bcancinov/4-channel-adc-module/step/EEHZA1E680XP.stp

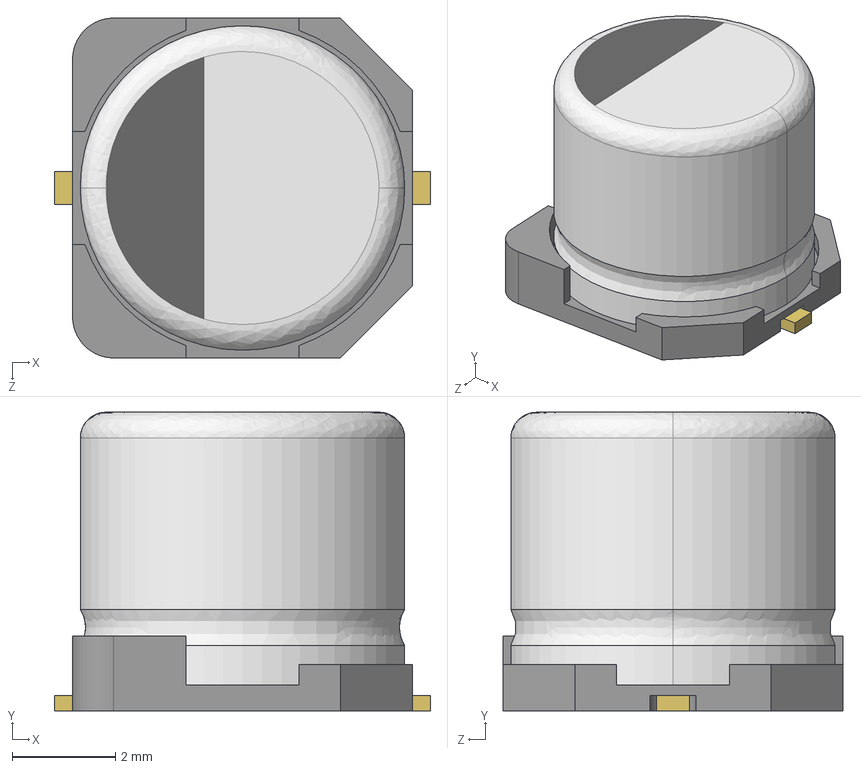
[picture p18: CAD file, 2025-04-16]
step/EEHZA1E680XP.stp
7.30 x 5.80 x 6.60 mm
•W€SIZE CODE D-001_1
•W€SIZE CODE D-002_1
•W€SIZE CODE D-003_1 x 2
