bcancinov/4-channel-adc-module/step/LFCSP16_ADA4945-1ACPZ-R2_ADI.step

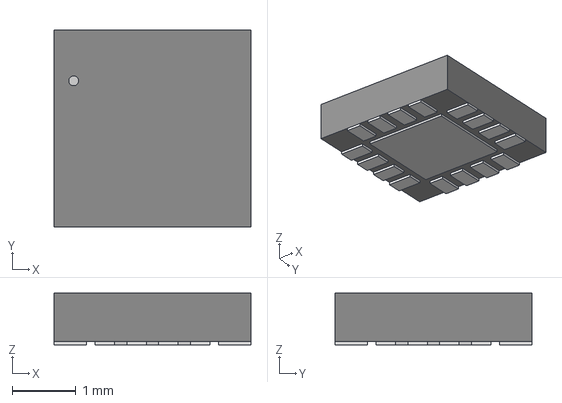
[picture p19: CAD file, 2025-04-16]
step/LFCSP16_ADA4945-1ACPZ-R2_ADI.step
3.10 x 3.10 x 0.815 mm
