bcancinov/4-channel-adc-module/step/24LC16BT-I_OT.stp

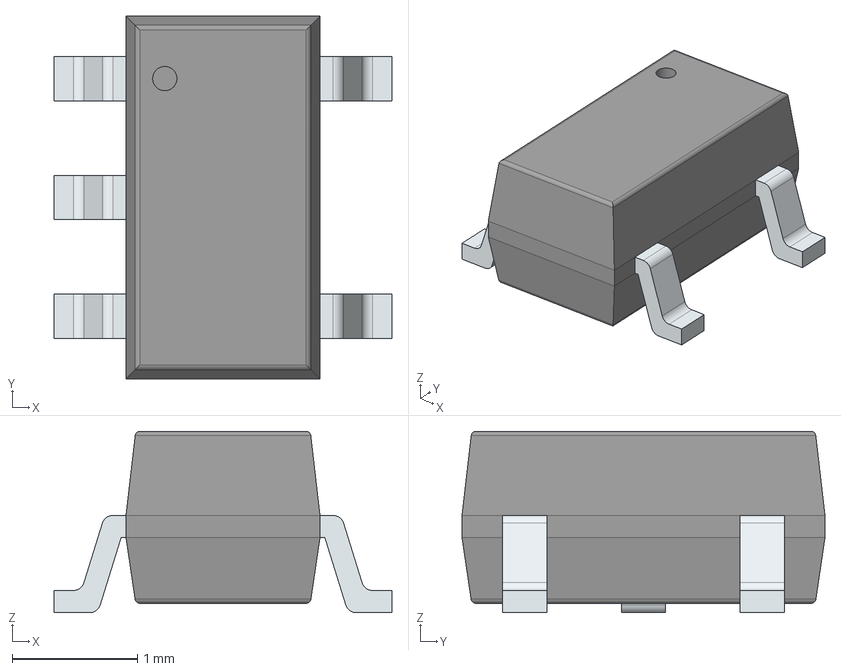
[picture p20: CAD file, 2025-04-16]
step/24LC16BT-I_OT.stp
2.70 x 2.90 x 1.45 mm
PinsArrayL
PinsArrayR
