bcancinov/4-channel-adc-module/step/LTC2387-18.step

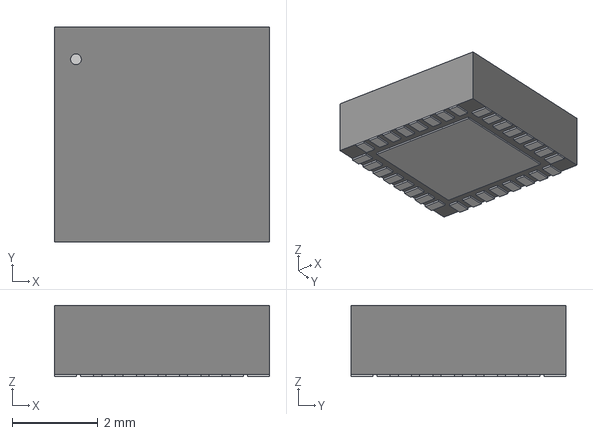
[picture p21: CAD file, 2025-04-16]
step/LTC2387-18.step
5.00 x 5.00 x 1.65 mm
