bcancinov/4-channel-adc-module/step/ECS-2520MVLC-120-CN-TR.stp

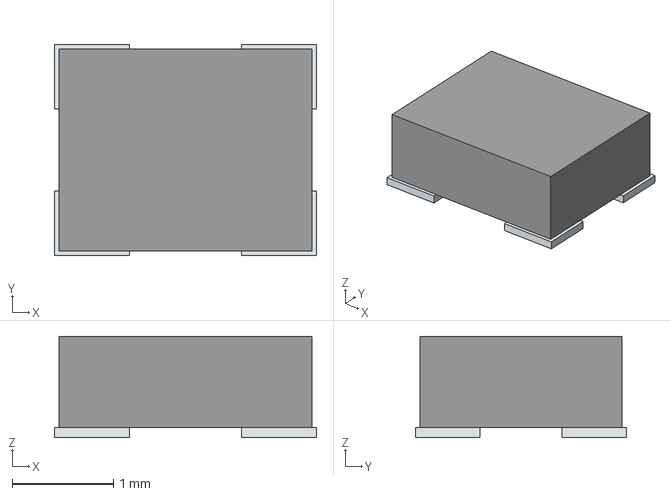
[picture p22: CAD file, 2025-04-16]
step/ECS-2520MVLC-120-CN-TR.stp
2.59 x 2.09 x 1.00 mm
Pins
