bcancinov/4-channel-adc-module/step/PJ-202AH.step

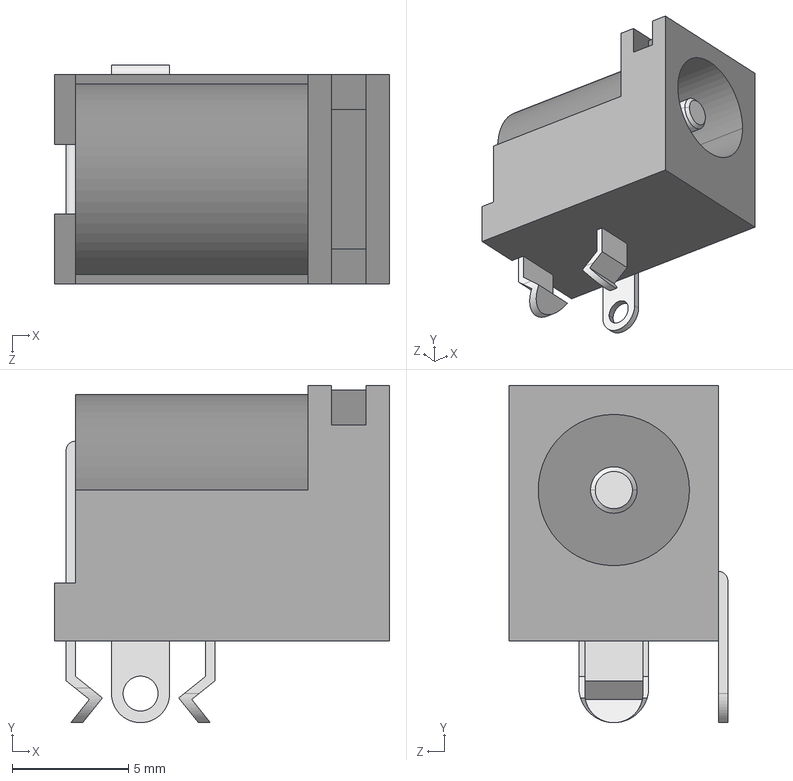
[picture p23: CAD file, 2025-04-16]
step/PJ-202AH.step
14.4 x 14.5 x 9.40 mm
