bcancinov/4-channel-adc-module/step/Coilcraft-XGL1010.step

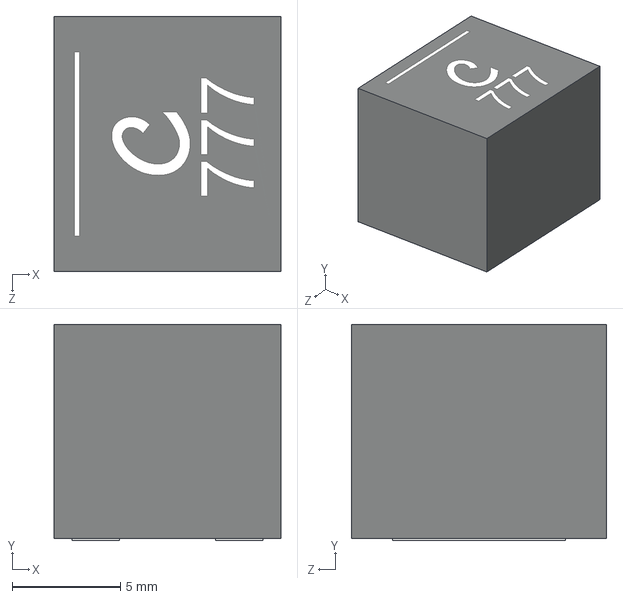
[picture p24: CAD file, 2025-04-16]
step/Coilcraft-XGL1010.step
10.5 x 10.0 x 11.8 mm
