bcancinov/4-channel-adc-module/step/LSHM-130-04.0-L-DV-A-S-K-TR.stp

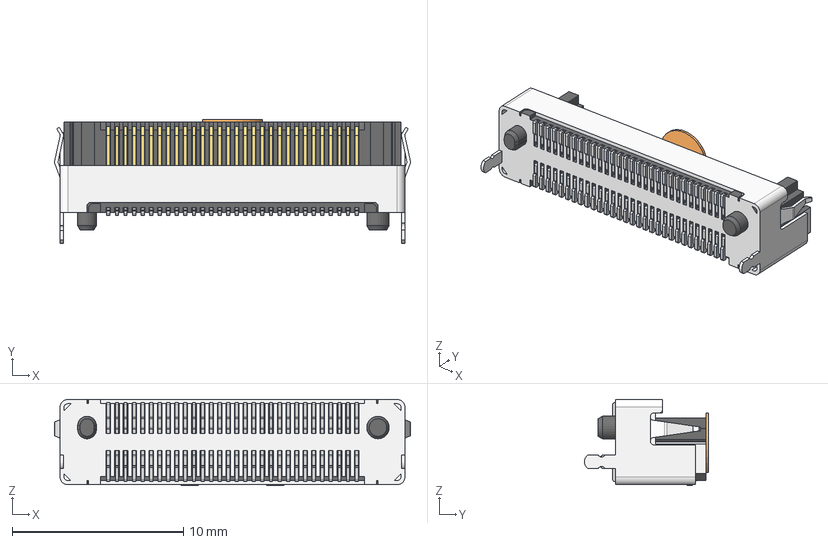
[picture p25: CAD file, 2025-04-16]
step/LSHM-130-04.0-L-DV-A-S-K-TR.stp
20.8 x 7.25 x 5.03 mm
LSHM-30-04.0-DV-A-S_STRIP
C-185--30-04.0-L-DV1P
C-185--30-04.0-DV1P2 L
K-DOT-.138-.250-.005.pp
