bcancinov/4-channel-adc-module/step/WE-CNSW-HF-0805_rev1.stp

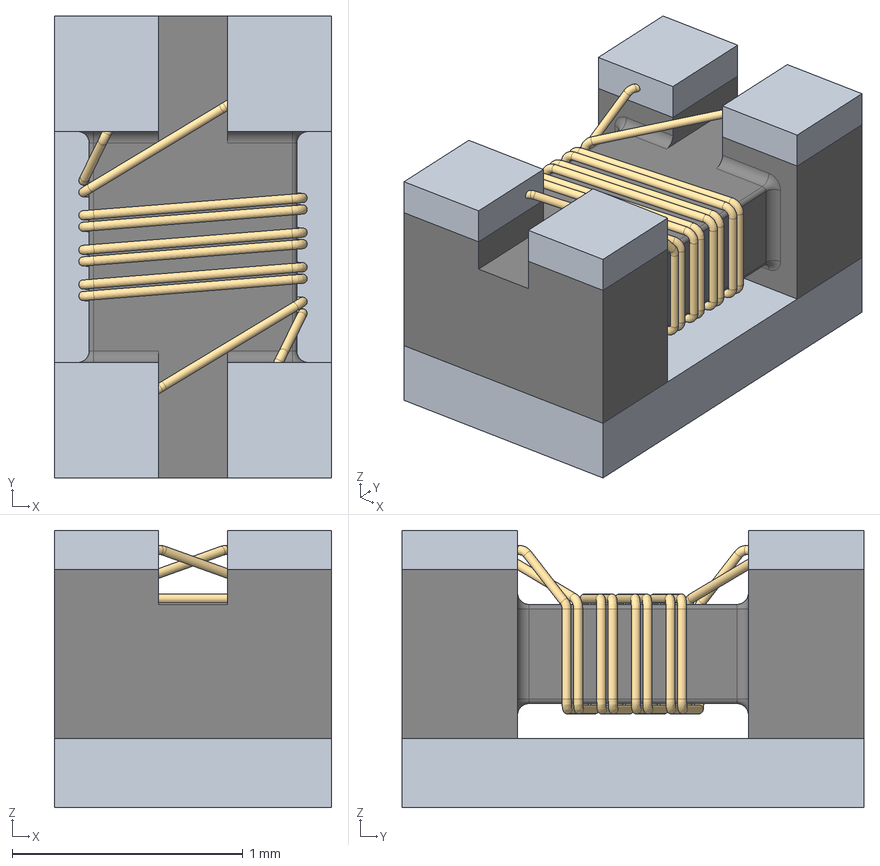
[picture p26: CAD file, 2025-04-16]
step/WE-CNSW-HF-0805_rev1.stp
1.20 x 2.00 x 1.20 mm
