bcancinov/4-channel-adc-module/step/TMJG4820GENL.STEP

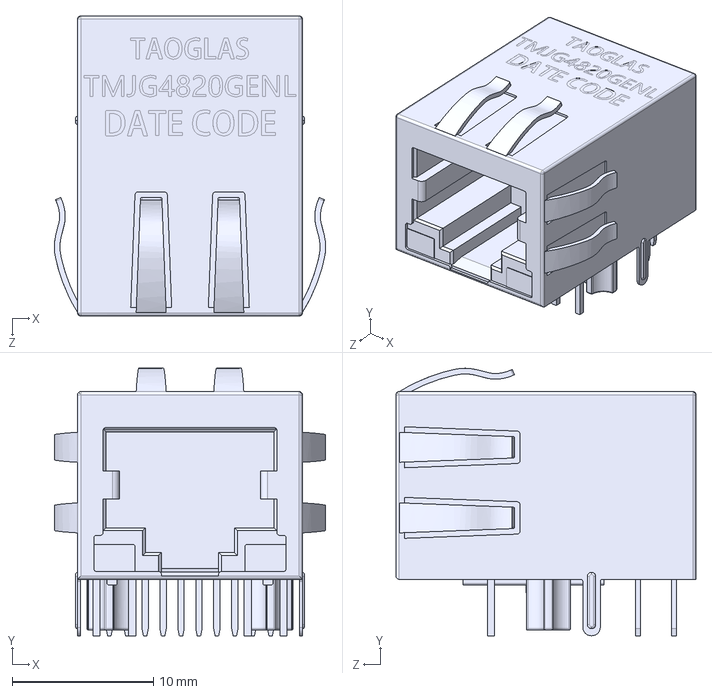
[picture p27: CAD file, 2025-04-16]
step/TMJG4820GENL.STEP
19.2 x 18.9 x 21.2 mm
