bcancinov/4-channel-adc-module/step/6-534998-0.stp

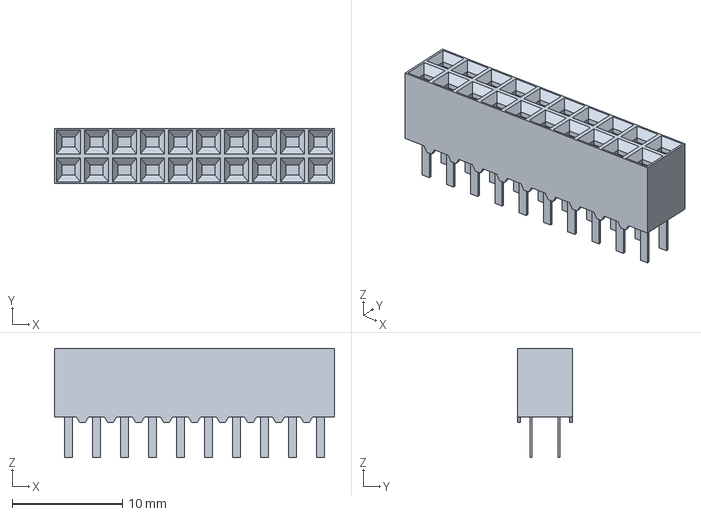
[picture p28: CAD file, 2025-04-16]
step/6-534998-0.stp
25.4 x 5.03 x 9.91 mm
