bcancinov/4-channel-adc-module/manual/sections/clock_gen/fig_clock_gen.pdf

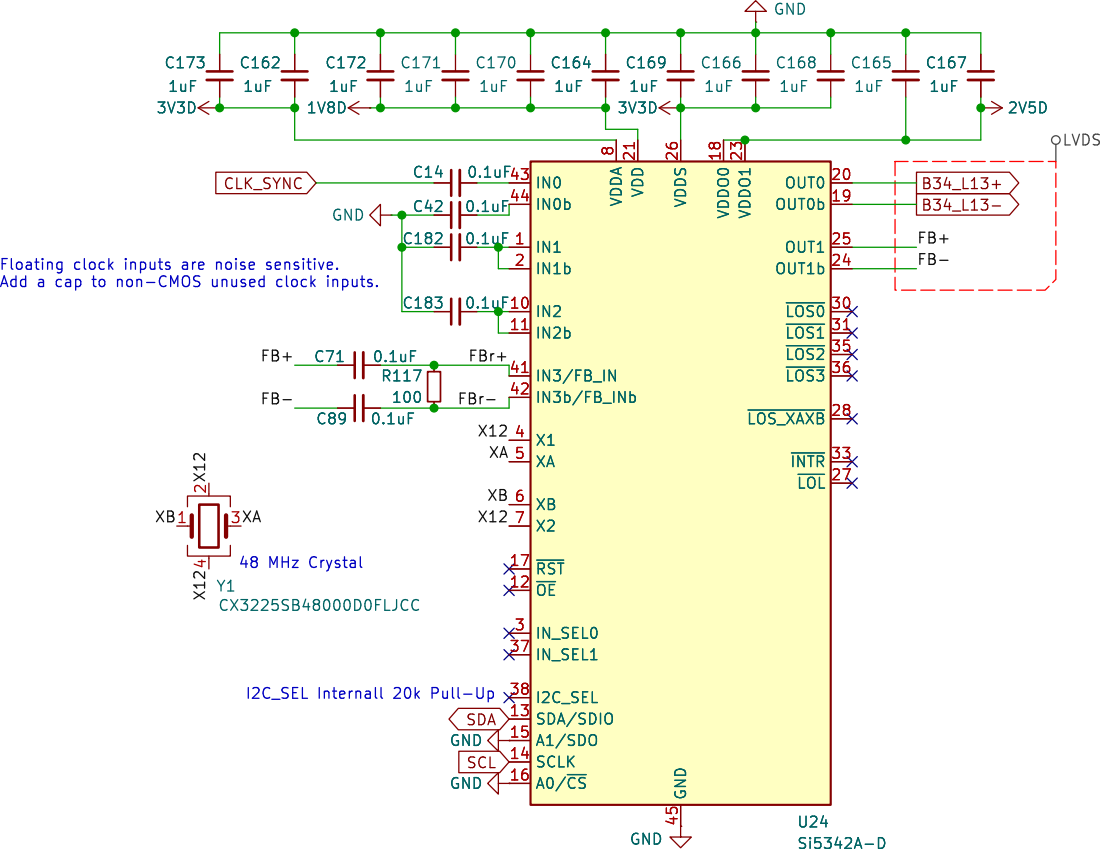
[picture p70: page 1]
