bcancinov/4-channel-adc-module/manual/sections/front_end_adc/fig_front_end_adc.pdf

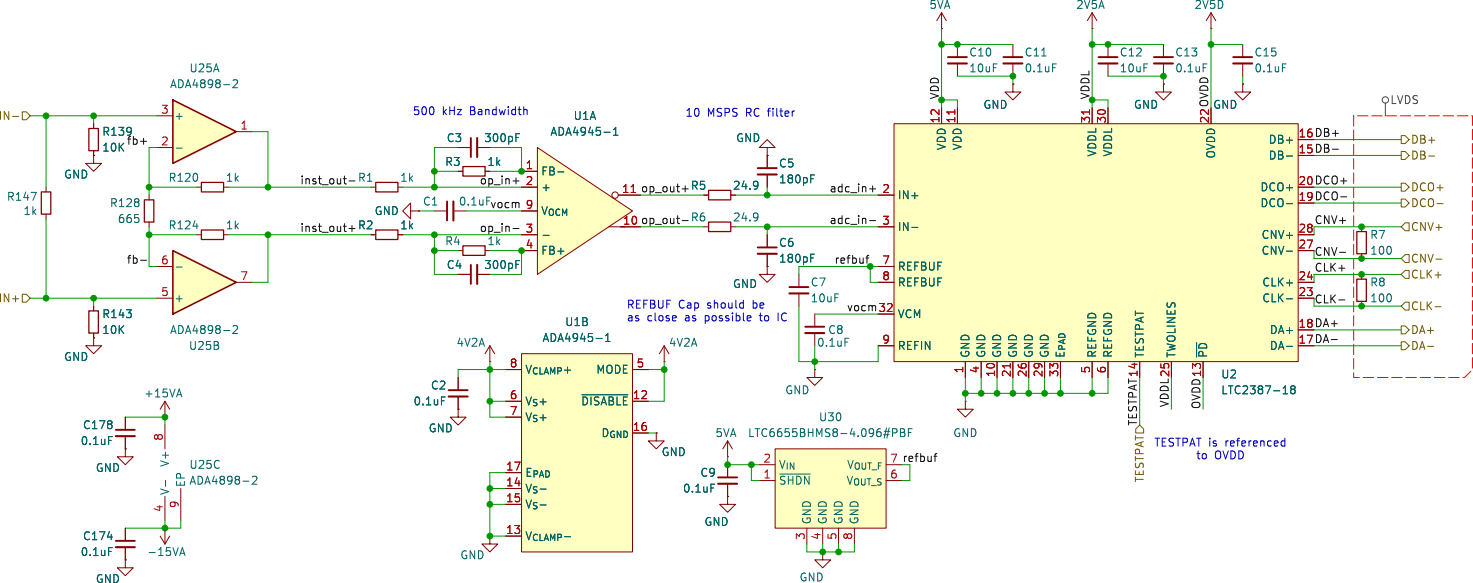
[picture p71: page 1]
