bcancinov/4-channel-adc-module/manual/sections/power/fig_12vin.pdf

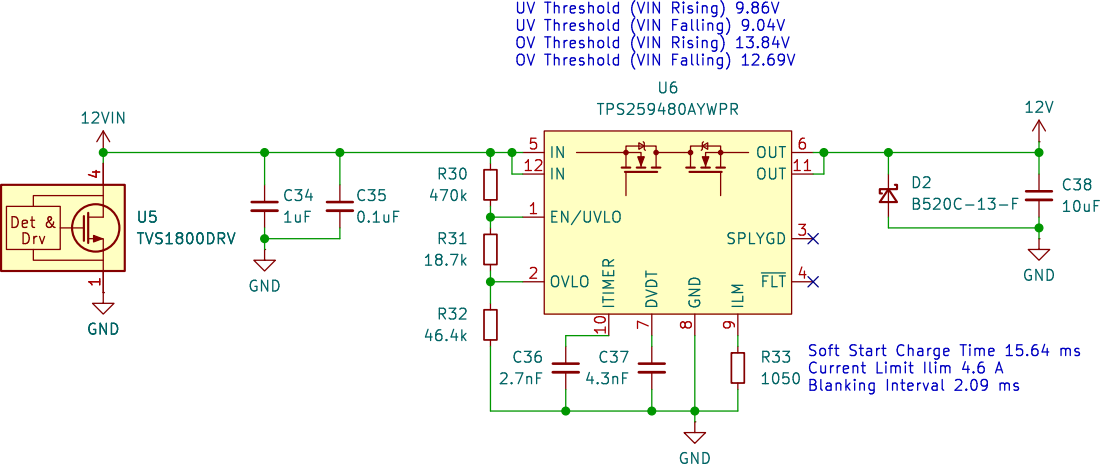
[picture p72: page 1]
