bcancinov/4-channel-adc-module/manual/sections/power/fig_15v5a.pdf

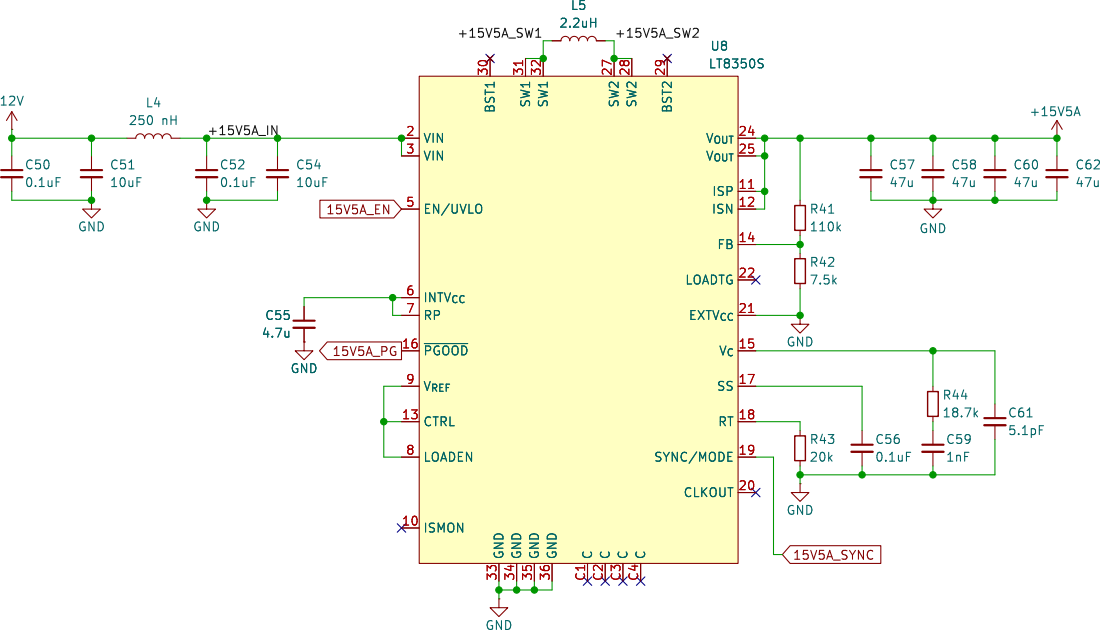
[picture p73: page 1]
