bcancinov/4-channel-adc-module/manual/sections/power/fig_3v3d.pdf

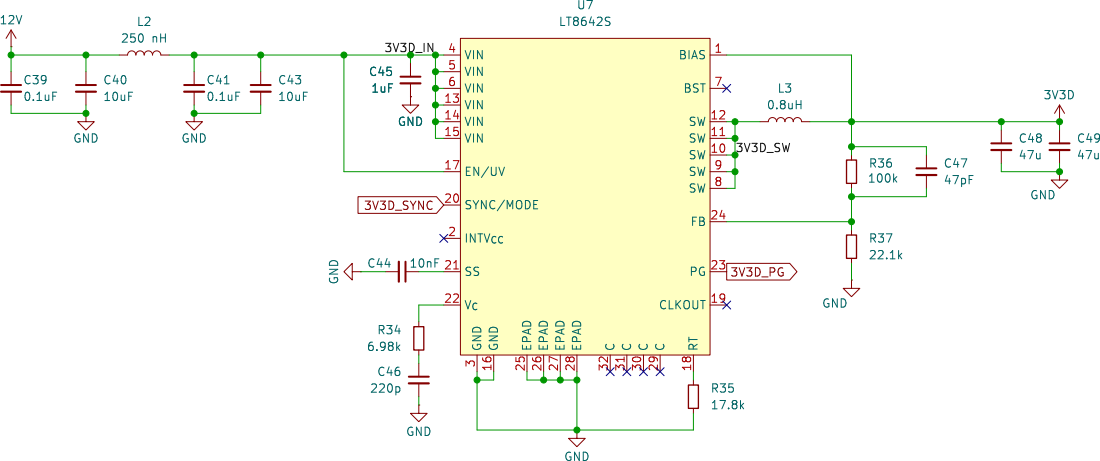
[picture p74: page 1]
