bcancinov/4-channel-adc-module/manual/sections/power/fig_5v5a.pdf

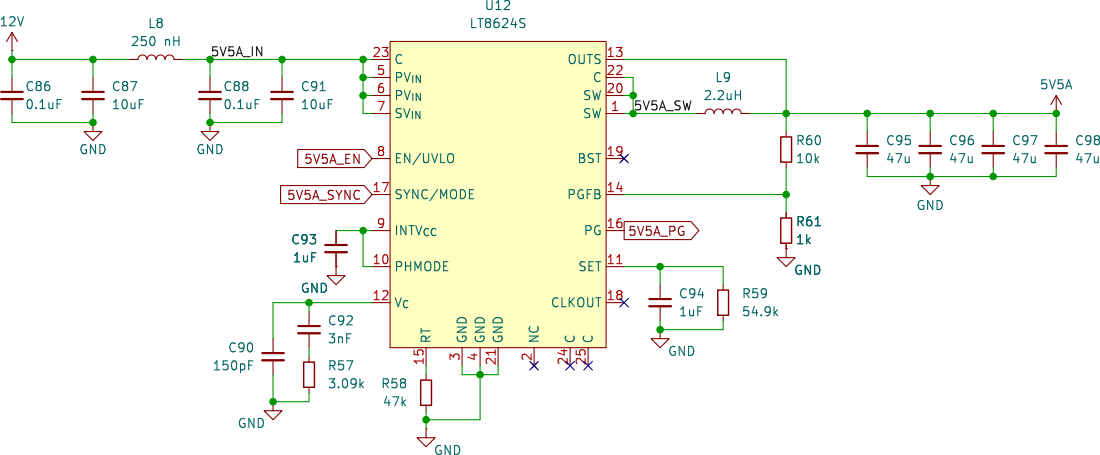
[picture p75: page 1]
