bcancinov/4-channel-adc-module/manual/sections/power/fig_5va.pdf

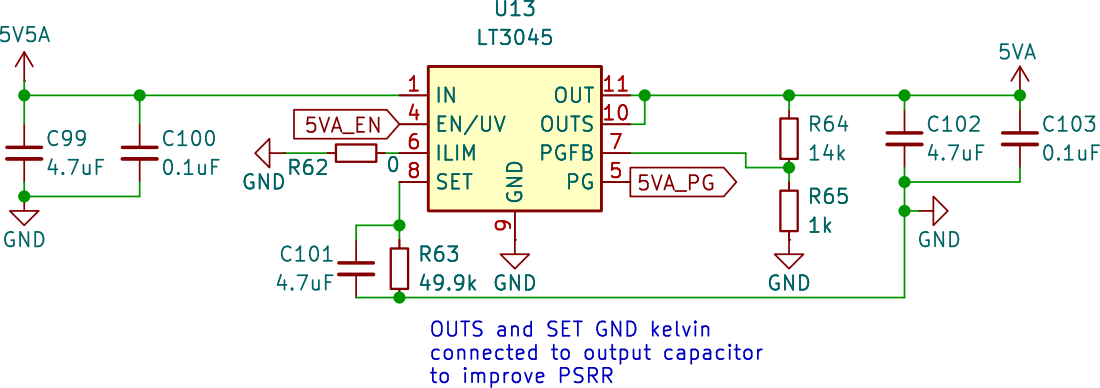
[picture p76: page 1]
