bcancinov/4-channel-adc-module/manual/sections/power/fig_n15v5a.pdf

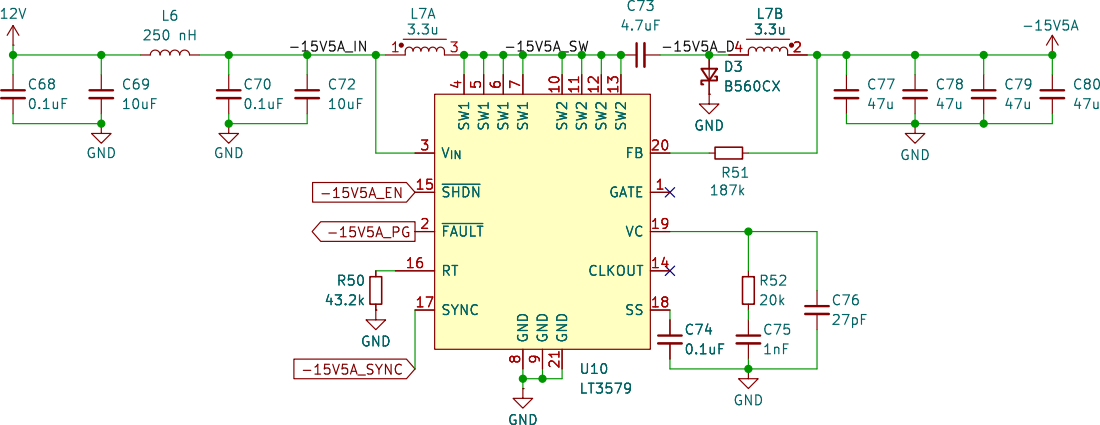
[picture p77: page 1]
