bcancinov/4-channel-adc-module/sim/adc_filter/settling_cap.asc

C1: cap; 160p
C2: cap; 2p
C3: cap; 18p
R1: res; 24.9
R2: res; 10
R3: res; 28
V1: voltage; 1
Named nets: 0, v1, v2, vo, vi
.ic v(v1)=0 v(v2)=0 v(vo)=0
.tran 1u
