bcancinov/4-channel-adc-module/sim/N15VA/Draft1.asc

C1: cap; 47n
J1: njf; LSK489A
R1: res; 1Meg
R2: res; 15k
V1: voltage; 15
V2: voltage; -15
V3: voltage; 0; AC 1
Named nets: 0, p15, n15, in, vsource
.tran 0 '100/fin' 0
.ic v(in)=-1
.param fin=1e-1
