bcancinov/4-channel-adc-module/sim/3V3D/3v3d.asc

C1: cap; 1n
Cff: cap; 47p
CinB: polcap; 68µ; x1; Rser=30m Lser=2.8n
CinC: cap; 5.65µ; x1; Rser=4m Lser=0.672n
CoutB: polcap; 0µ; x0; Rser=0m Lser=0n
CoutC: cap; 47µ; x2; Rser=2.172m Lser=0.204n
Cth: cap; 220p
I1: current; PWL(0 0 1m 0 1.0001m 1 1.2m 1 1.2001m 0)
L1: ind; 0.8µ; Rser=0.88m
R1: res; 3.3
Rb: res; 22.1k
Rosc: res; 17.8k
Rt: res; 100k
Rth: res; 6.98k
U1: LT8642S
V1: voltage; 12V
Named nets: 0, Vin, vout
.tran 1.5m startup
LT8642S - 18V, 10A Synchronous Step-Down Silent Switcher 2
