bcancinov/4-channel-adc-module/sim/5V5A/5v5a.asc

C1: cap; 100n
C2: cap; 1µF
Cinb1: cap; 0µF; x0; Rser=0m Lser=0n
Cinc1: cap; 5.55µF; x1; Rser=4.83m Lser=0.83n
Coc1: cap; 40.66µF; x4; Rser=2.17m Lser=0.2n
Cth1: cap; 3000pF
Cthp1: cap; 150pF
L1: ind; 2.2µH; Rser=1.4m
Load1: current; PWL(0 0 1m 0 1.0001m 0.5 1.2m 0.5 1.20001m 1 1.4m 1 1.40001m 1.5 1.6m 1.5 1.60001m 2)
R1: res; 10k
R2: res; 1k
R3: res; 100k
R4: res; 100
Rb1: res; 100000k
Rfreq1: res; 47k
Riset1: res; 54.9k
Rt1: res; 0.001k
Rth1: res; 3.09k
U1: LT8624S
Vin1: voltage; 12V
Named nets: 0, SW, PGFB, SET, VOUT1
LT8624S - 18V, 4A Synchronous Step-Down Silent Switcher with Ultralow Noise Reference
.tran 2m startup
* Adjust R1,R2,C1 as desired for start-up timing
Designer:
Date:
ProjectName:
