bcancinov/4-channel-adc-module/sim/N15VA/n15va.asc

C1: cap; 4.7µ
C2: cap; 0.1µ
C3: cap; 1n
C4: cap; 27p
Coc2: cap; 12.84µ; x4; Rser=2.172m Lser=0.204n
D1: diode; B560C
I1: current; PWL(0 0 10m 0 10.0001m 0.5 12m 0.5 12.0001m 1 14m 1 14.0001m 1.5)
L1: ind; 3.3µ; Rser=6.3m
L2: ind; 3.3µ; Rser=6.3m
R1: res; 100k
R2: res; 20k
R3: res; 187k
R4: res; 43.2k
R5: res; 100
U1: LT3579
V1: voltage; 12
Named nets: 0
.tran 16m startup
K1 L1 L2 0.98
