bcancinov/4-channel-adc-module/sim/P15VA/p15va.asc

C1: cap; 15p
C2: cap; 1000p
C3: cap; 1µ
C4: cap; 5.1p
C8: cap; 10n
CfbBot1: cap; 0p
CfbTop1: cap; 0p
Cinb1: cap; 0µ; x0
Cinc1: cap; 4.45µ; x1
Cob1: cap; 0µ; x0; Rser=0m Lser=0n
Coc1: cap; 12.84µ; x4; Rser=2.172m Lser=0.204n
Lo1: ind; 2.2µ; Rser=1.4m
LoadStep1: current; PWL(0 0 1.4m 0 1.4001m 0.5 1.6m 0.5 1.6001m 1)
R1: res; 100k
R2: res; 499k
R3: res; 80k
R4: res; 18.7k
R5: res; 100
RfbBot1: res; 7.5k
RfbTop1: res; 110k
Rfreq_1: res; 20k
U1: LT8350S
Vin1: voltage; 13V
Named nets: 0, OUT, IN
.tran 2.5m startup
If simulation model is not found, please "Sync release".
LT8350S - 40Vin, 18Vout, 6A Synchronous Buck-Boost Silent Switcher
